kwame-y/PCBCard/images/Screenshot 2026-05-23 at 15.53.15.png

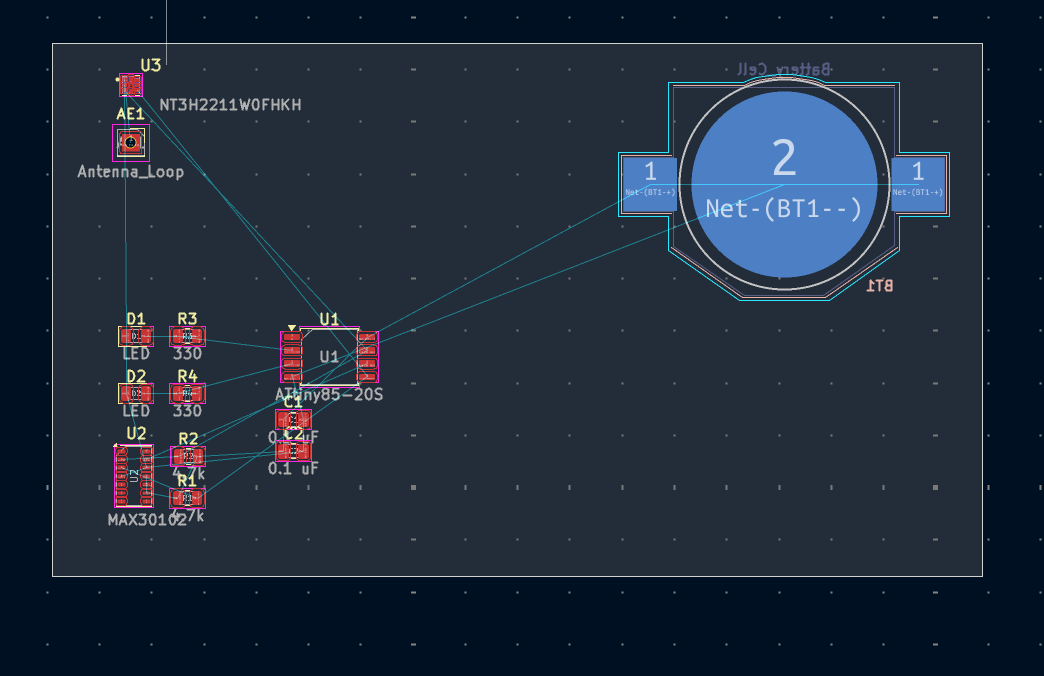
images/Screenshot 2026-05-23 at 15.53.15.png
