kwame-y/PCBCard/Hardware/PCBCard.kicad_sch

## KiCad design Hardware/PCBCard.kicad_sch (2026-06-12)

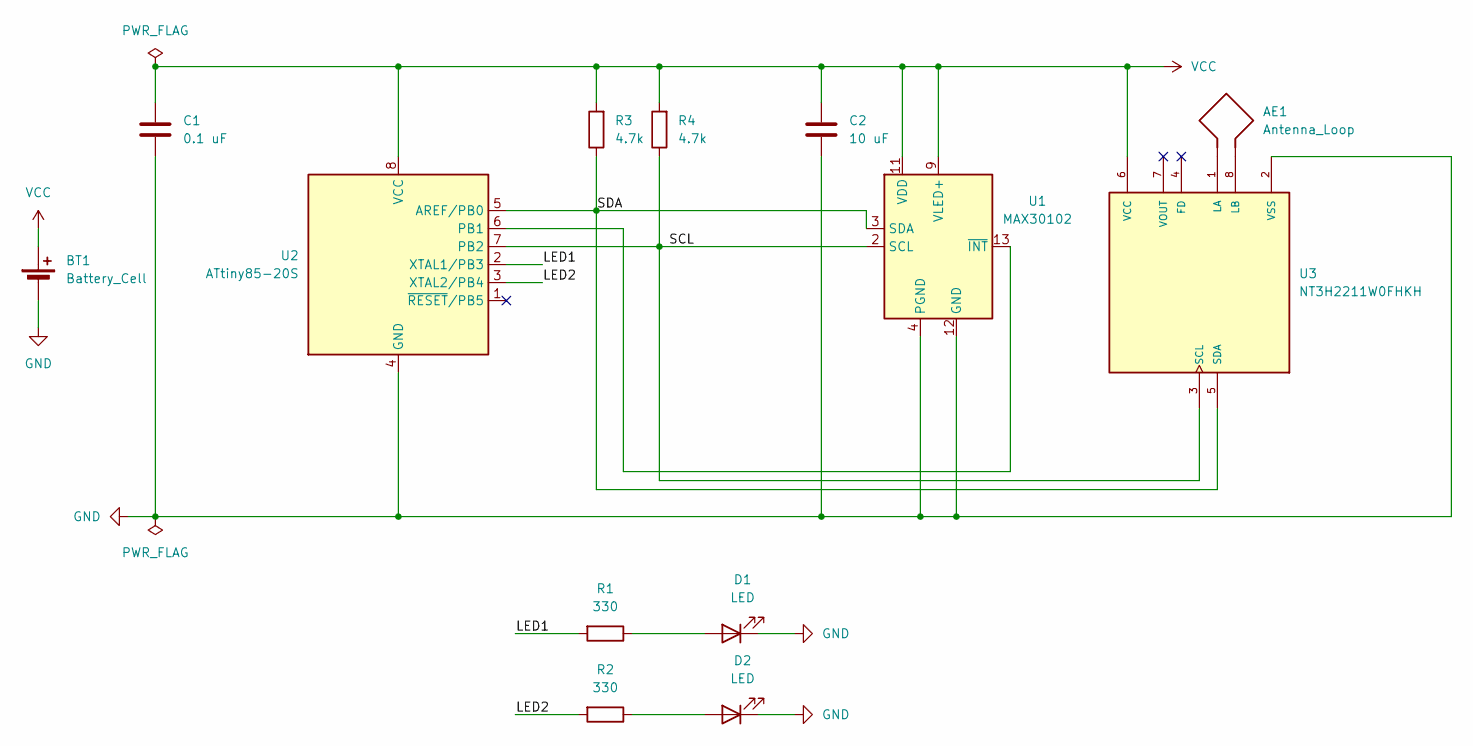
[picture p16: schematic PCBCard.kicad_sch]

Parts:
AE1: Antenna_Loop; PinHeader_1x01_P2.54mm_Vertical
BT1: Battery_Cell; BatteryHolder_Keystone_3002_1x2032
C1: 0.1 uF; C_0805_2012Metric
C2: 10 uF; C_0805_2012Metric
D1, D2: LED; LED_0805_2012Metric
R1, R2: 330; R_0805_2012Metric
R3, R4: 4.7k; R_0805_2012Metric
U1: MAX30102; Maxim_OLGA-14_3.3x5.6mm_P0.8mm
U2: ATtiny85-20S; SOIC-8_3.9x4.9mm_P1.27mm
U3: NT3H2211W0FHKH; IC_NT3H2211W0FHKH; PARTREV 3.4

Connections:
GND: BT1.2 (-), C1.2, C2.2, D1.1 (K), D2.1 (K), U1.4 (PGND), U1.12 (GND), U2.4 (GND), U3.2 (VSS)
LED1: R1.2, U2.2 (XTAL1/PB3)
LED2: R2.2, U2.3 (XTAL2/PB4)
unnamed: AE1.1, U3.1 (LA)
unnamed: AE1.2, U3.8 (LB)
unnamed: D1.2 (A), R1.1
unnamed: D2.2 (A), R2.1
unnamed: U1.13 (~INT), U2.6 (PB1)
SCL: R4.1, U1.2 (SCL), U2.7 (PB2), U3.3 (SCL)
SDA: R3.1, U1.3 (SDA), U2.5 (AREF/PB0), U3.5 (SDA)
VCC: BT1.1 (+), C1.1, C2.1, R3.2, R4.2, U1.9 (VLED+), U1.10 (VLED+), U1.11 (VDD), U2.8 (VCC), U3.6 (VCC)
